AKEB/watercounter/IMG_0184.JPG

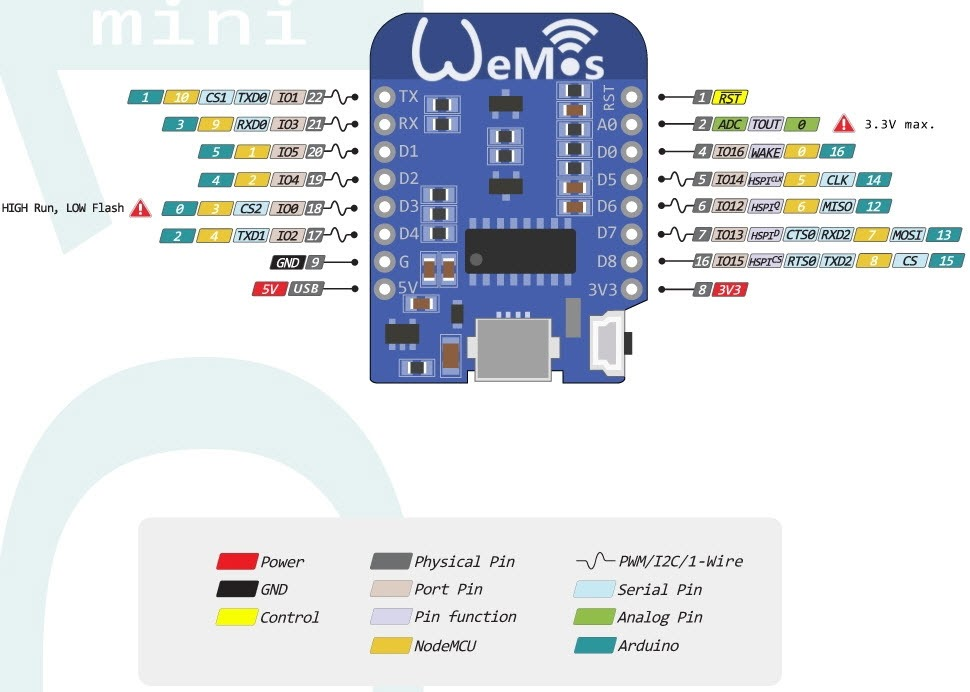
IMG_0184.JPG
