AKEB/watercounter/Photos/IMG_0148.JPG.jpeg

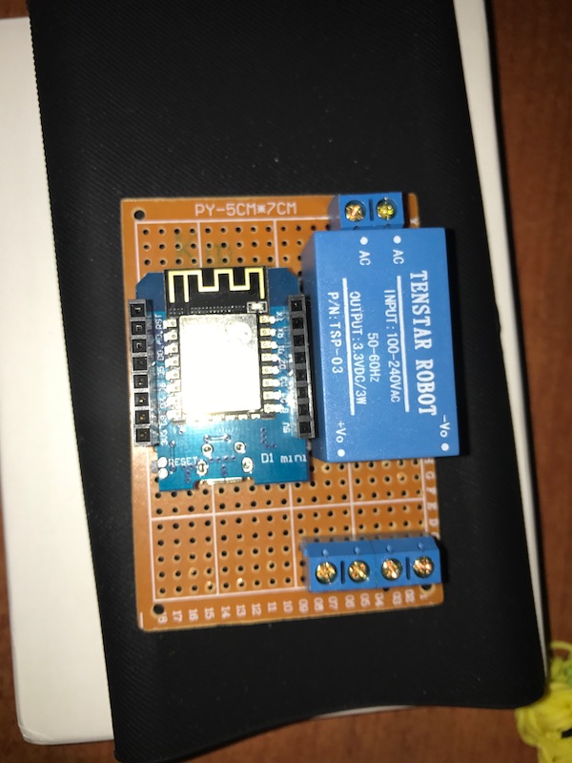
Photos/IMG_0148.JPG.jpeg
