AKEB/watercounter/Photos/IMG_0178.PNG.png

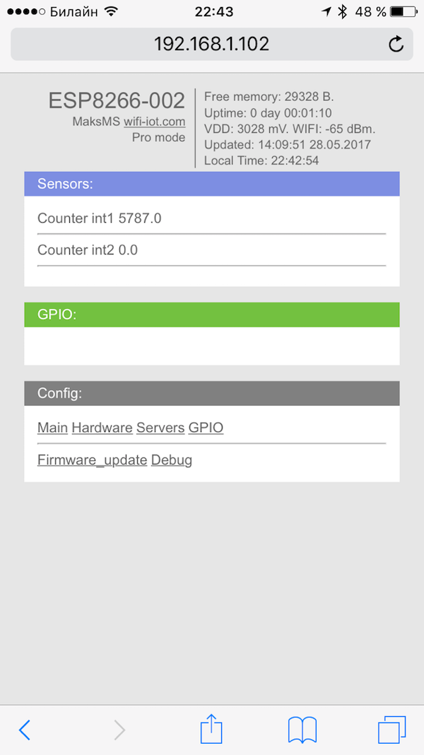
Photos/IMG_0178.PNG.png
