AKEB/watercounter/Photos/IMG_0179.JPG.jpeg

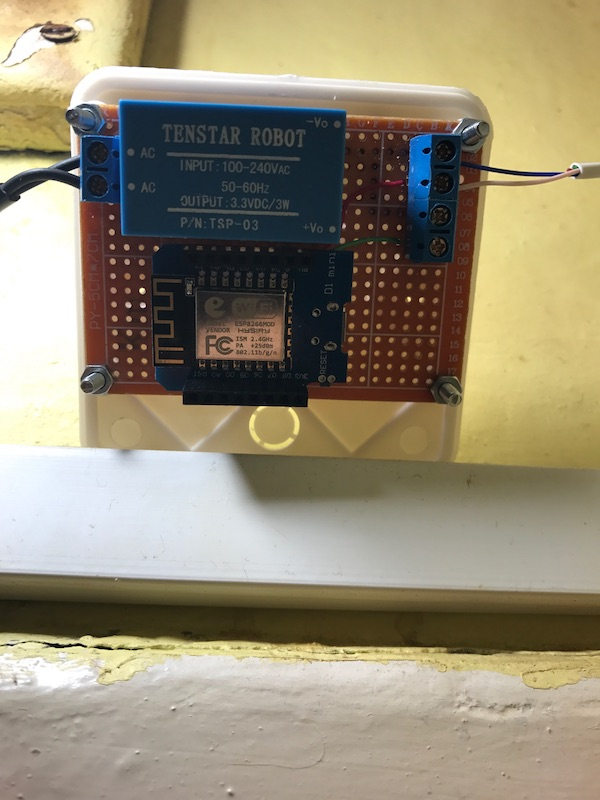
Photos/IMG_0179.JPG.jpeg
