AKEB/watercounter/Photos/IMG_0180.JPG.jpeg

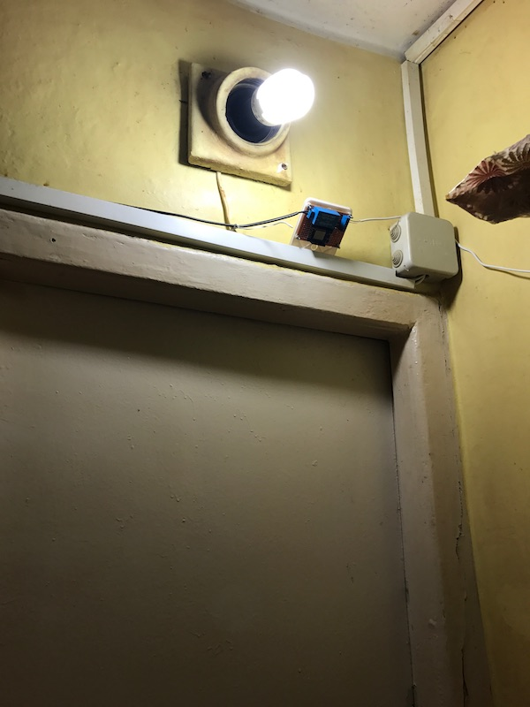
Photos/IMG_0180.JPG.jpeg
