AKEB/watercounter/Photos/IMG_0183.PNG

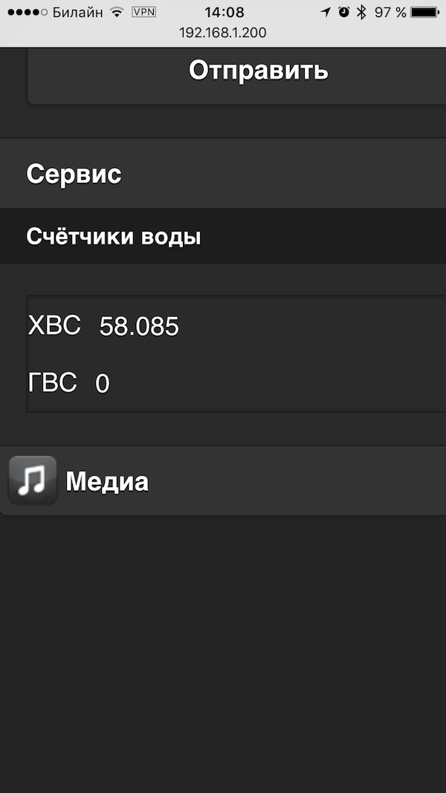
Photos/IMG_0183.PNG
