AKEB/watercounter/Photos/IMG_0248.jpg

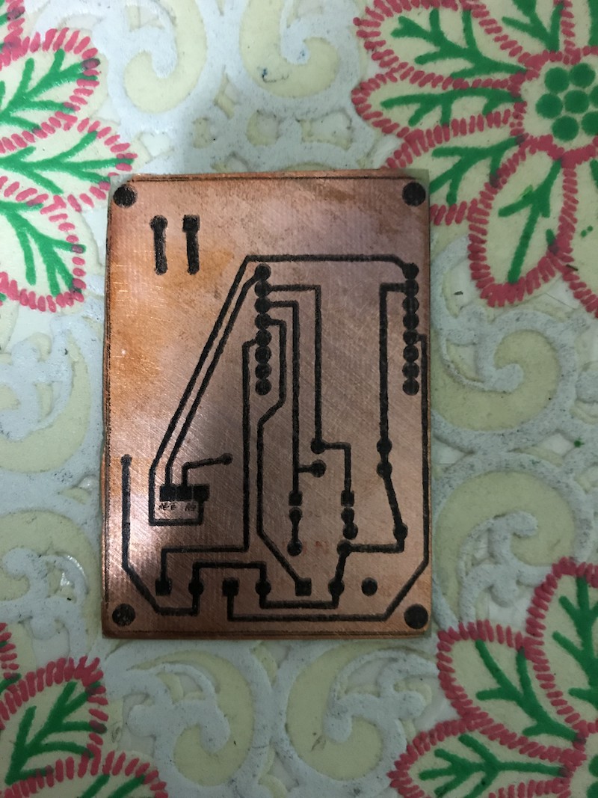
Photos/IMG_0248.jpg
