AKEB/watercounter/Photos/IMG_0249.jpg

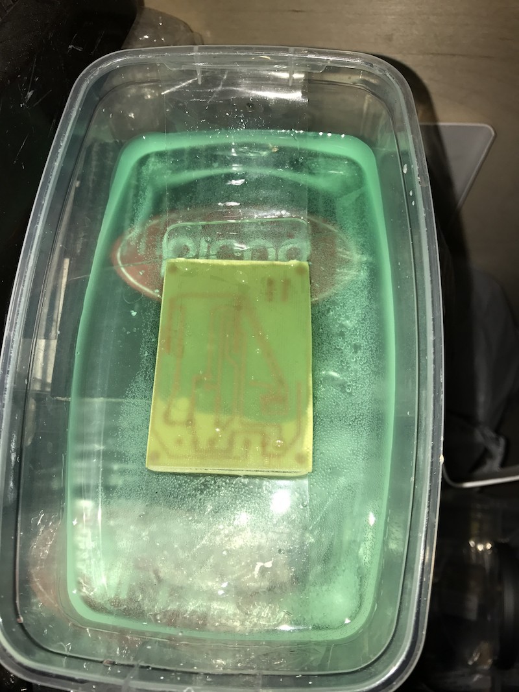
Photos/IMG_0249.jpg
