AKEB/watercounter/Photos/IMG_0250.jpg

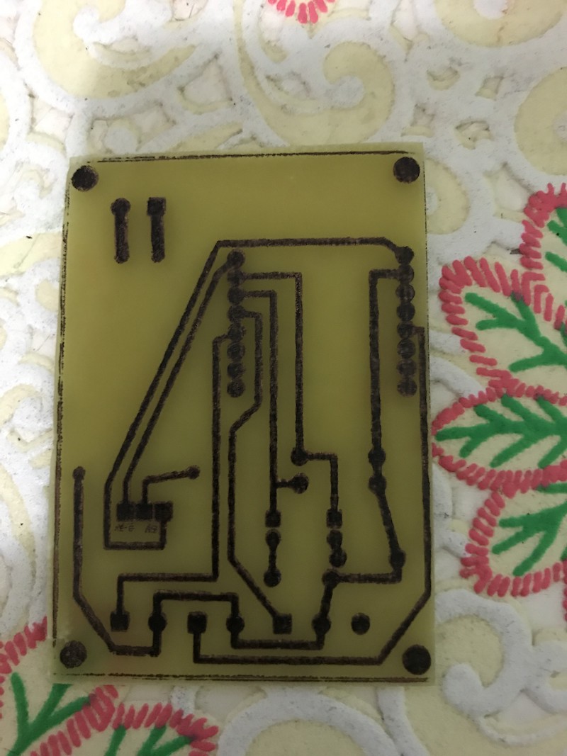
Photos/IMG_0250.jpg
