AKEB/watercounter/Photos/IMG_0251.jpg

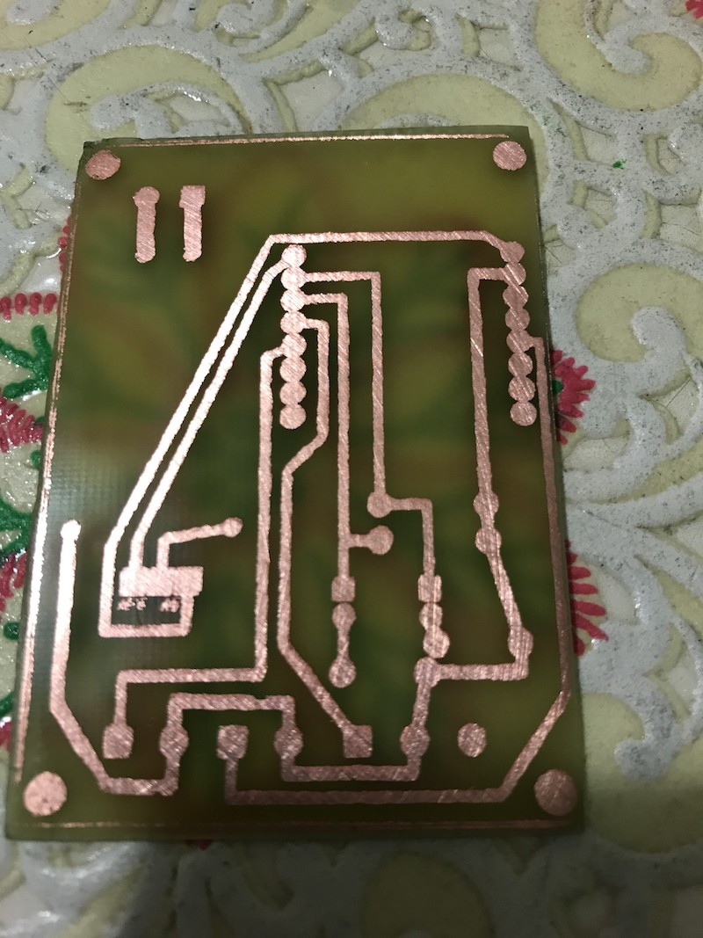
Photos/IMG_0251.jpg
