AKEB/watercounter/Photos/IMG_0252.jpg

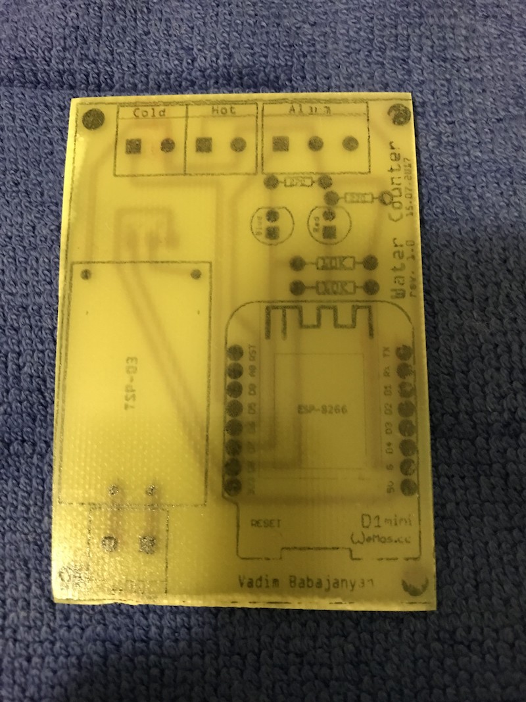
Photos/IMG_0252.jpg
