AKEB/watercounter/Photos/IMG_0253.jpg

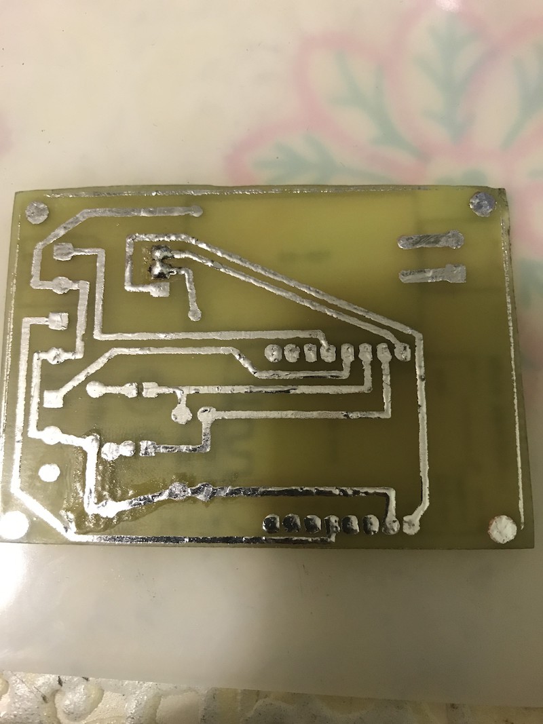
Photos/IMG_0253.jpg
