AKEB/watercounter/Photos/IMG_0255.jpg

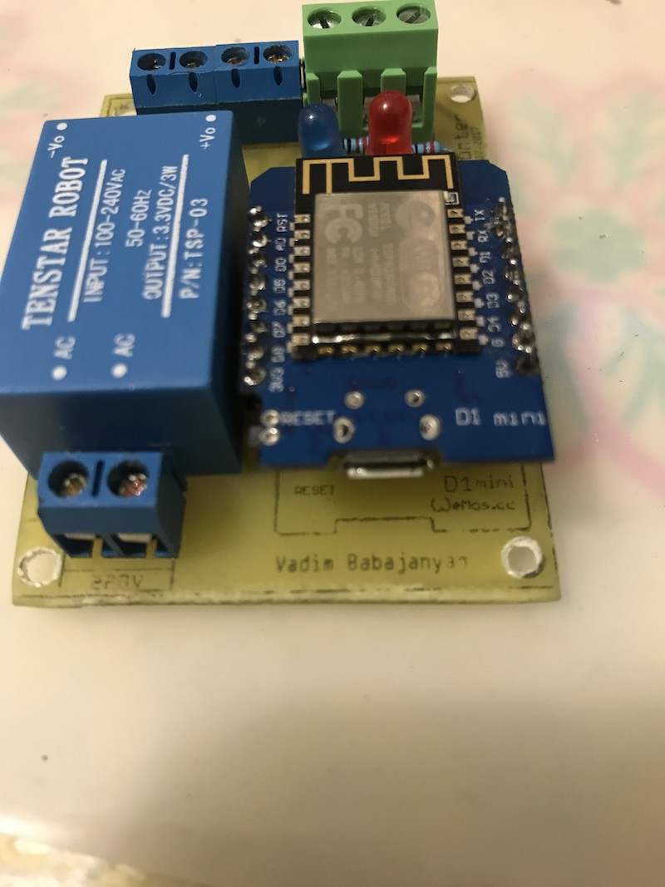
Photos/IMG_0255.jpg
