AKEB/watercounter/Photos/IMG_0256.jpg

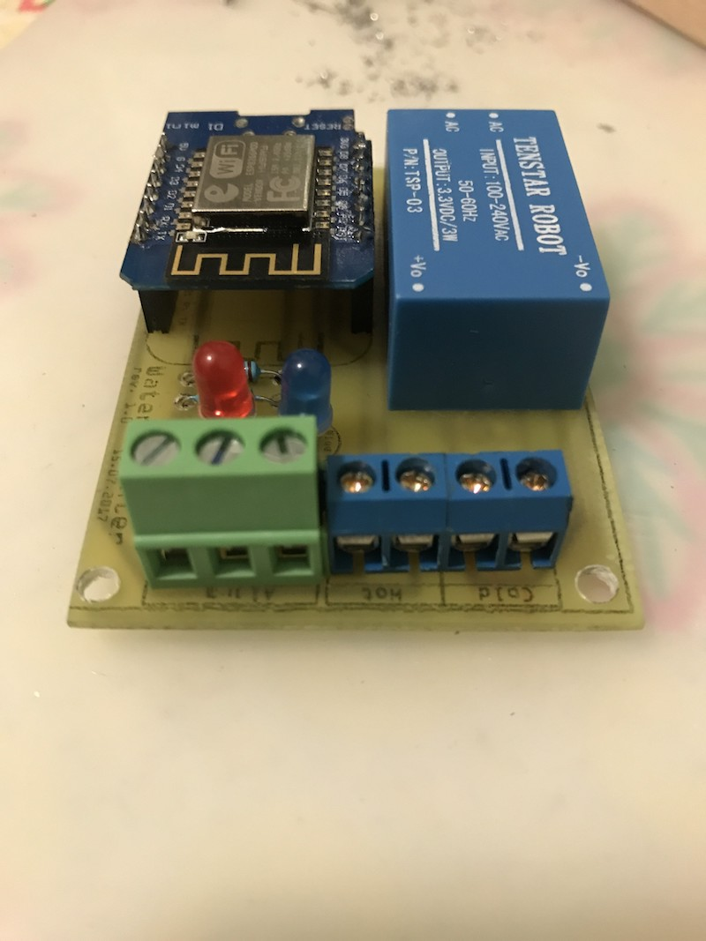
Photos/IMG_0256.jpg
