AKEB/watercounter/Photos/IMG_0257.jpg

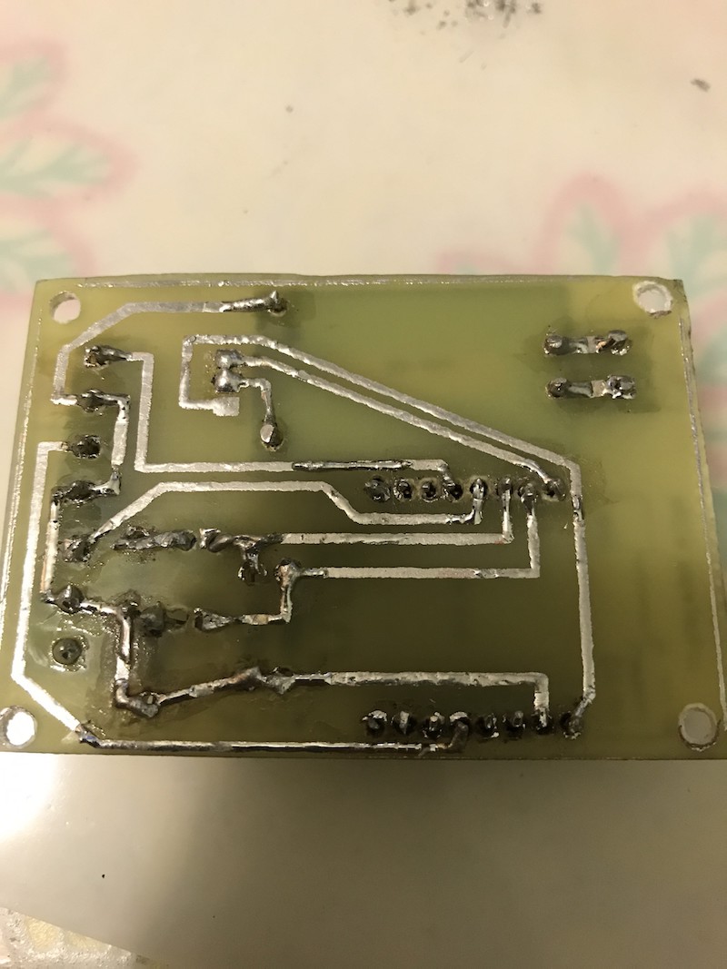
Photos/IMG_0257.jpg
