AKEB/watercounter/PCB/pdf/WaterCounter_etch_silk_bottom.pdf

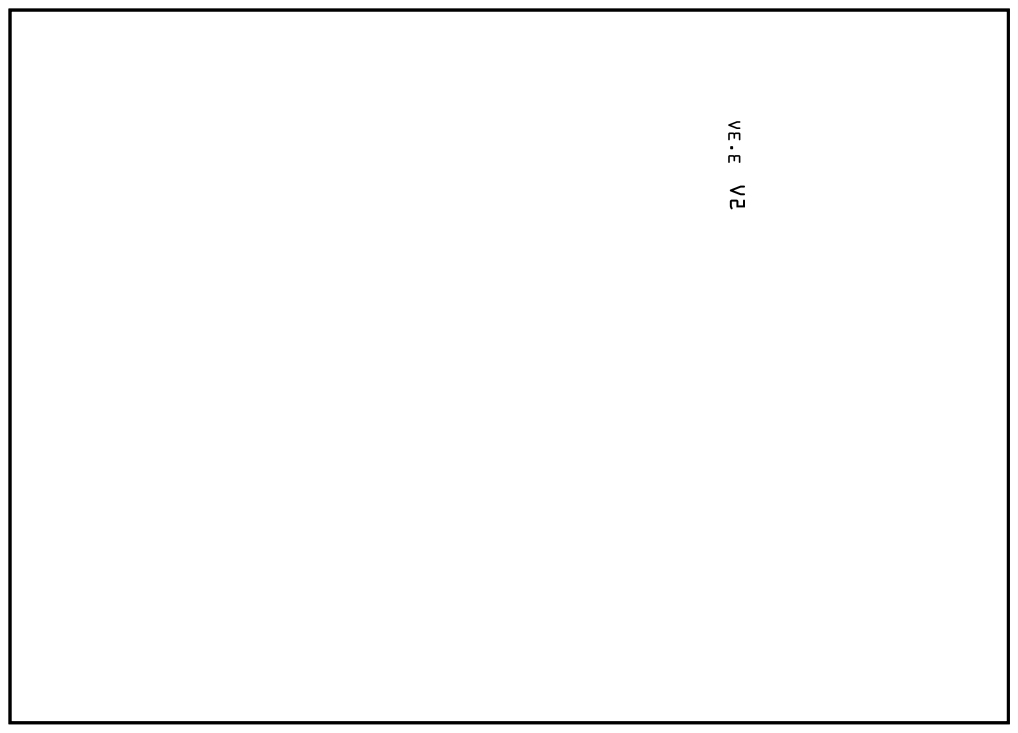
[picture p32: page 1]
