AKEB/watercounter/PCB/pdf/WaterCounter_etch_silk_bottom_mirror.pdf

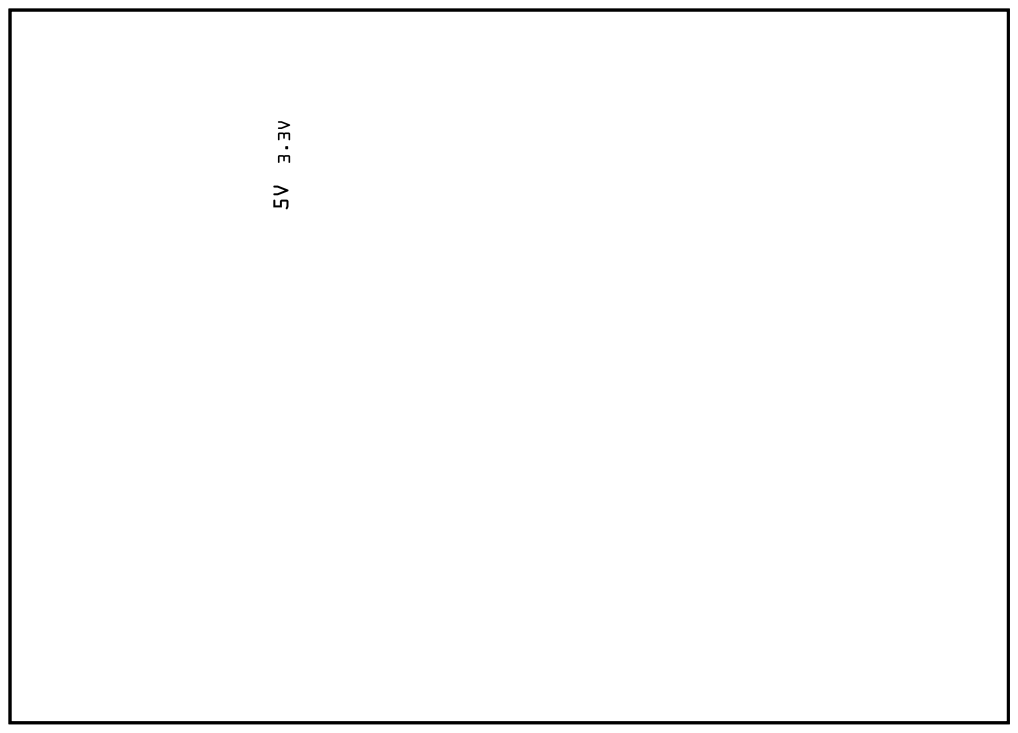
[picture p33: page 1]
