AKEB/watercounter/PCB/pdf/WaterCounter_etch_silk_top.pdf

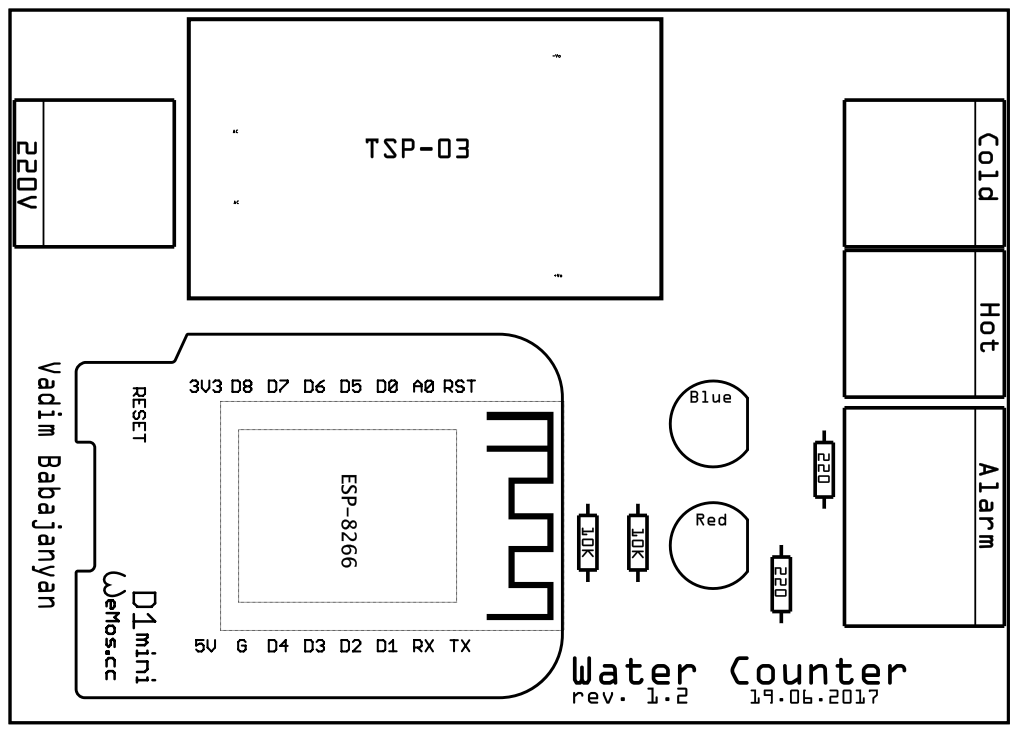
[picture p34: page 1]
