AKEB/watercounter/PCB/pdf/WaterCounter_etch_silk_top_mirror.pdf

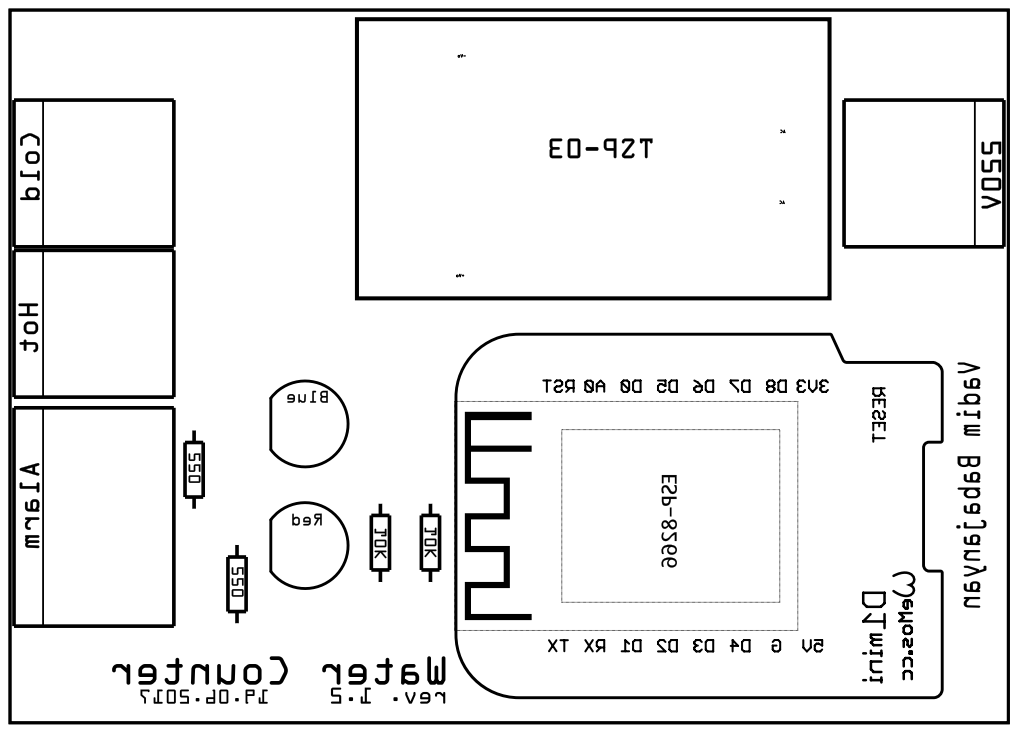
[picture p35: page 1]
