AKEB/watercounter/WaterCounter/FS.ino

// Инициализация FFS
void FS_init(void) {
	SPIFFS.begin();
	{
		Dir dir = SPIFFS.openDir("/");
		while (dir.next()) {
			String fileName = dir.fileName();
			size_t fileSize = dir.fileSize();
		}
	}
	//HTTP страницы для работы с FFS
	//list directory
	HTTP.on("/list", HTTP_GET, handleFileList);
	//загрузка редактора editor
	HTTP.on("/edit", HTTP_GET, []() {
		if(!HTTP.authenticate(_http_user.c_str(), _http_password.c_str())) return HTTP.requestAuthentication();
		if (!handleFileRead("/edit.html")) HTTP.send(404, "text/plain", "FileNotFound");
	});
	//Создание файла
	HTTP.on("/edit", HTTP_PUT, handleFileCreate);
	//Удаление файла
	HTTP.on("/edit", HTTP_DELETE, handleFileDelete);
	//first callback is called after the request has ended with all parsed arguments
	//second callback handles file uploads at that location
	HTTP.on("/edit", HTTP_POST, []() {
		HTTP.send(200, "text/plain", "");
	}, handleFileUpload);
	//called when the url is not defined here
	//use it to load content from SPIFFS
	HTTP.onNotFound([]() {
		if (!handleFileRead(HTTP.uri())) HTTP.send(404, "text/plain", "FileNotFound");
	});
}

// Здесь функции для работы с файловой системой
String getContentType(String filename) {
	if (HTTP.hasArg("download")) return "application/octet-stream";
	else if (filename.endsWith(".htm")) return "text/html";
	else if (filename.endsWith(".html")) return "text/html";
	else if (filename.endsWith(".json")) return "application/json";
	else if (filename.endsWith(".css")) return "text/css";
	else if (filename.endsWith(".js")) return "application/javascript";
	else if (filename.endsWith(".png")) return "image/png";
	else if (filename.endsWith(".gif")) return "image/gif";
	else if (filename.endsWith(".jpg")) return "image/jpeg";
	else if (filename.endsWith(".ico")) return "image/x-icon";
	else if (filename.endsWith(".xml")) return "text/xml";
	else if (filename.endsWith(".pdf")) return "application/x-pdf";
	else if (filename.endsWith(".zip")) return "application/x-zip";
	else if (filename.endsWith(".gz")) return "application/x-gzip";
	return "text/plain";
}

bool handleFileRead(String path) {
	if (path.endsWith("/")) path += "index.html";
	String contentType = getContentType(path);
	String pathWithGz = path + ".gz";
	if (SPIFFS.exists(pathWithGz) || SPIFFS.exists(path)) {
		if (SPIFFS.exists(pathWithGz)) path += ".gz";
		File file = SPIFFS.open(path, "r");
		size_t sent = HTTP.streamFile(file, contentType);
		file.close();
		return true;
	}
	return false;
}

void handleFileUpload() {
	if (HTTP.uri() != "/edit") return;
	HTTPUpload& upload = HTTP.upload();
	if (upload.status == UPLOAD_FILE_START) {
		String filename = upload.filename;
		if (!filename.startsWith("/")) filename = "/" + filename;
		fsUploadFile = SPIFFS.open(filename, "w");
		filename = String();
	} else if (upload.status == UPLOAD_FILE_WRITE) {
		//DBG_OUTPUT_PORT.print("handleFileUpload Data: "); DBG_OUTPUT_PORT.println(upload.currentSize);
		if (fsUploadFile) fsUploadFile.write(upload.buf, upload.currentSize);
	} else if (upload.status == UPLOAD_FILE_END) {
		if (fsUploadFile) fsUploadFile.close();
	}
}

void handleFileDelete() {
	if (HTTP.args() == 0) return HTTP.send(500, "text/plain", "BAD ARGS");
	String path = HTTP.arg(0);
	if (path == "/") return HTTP.send(500, "text/plain", "BAD PATH");
	if (!SPIFFS.exists(path)) return HTTP.send(404, "text/plain", "FileNotFound");
	SPIFFS.remove(path);
	HTTP.send(200, "text/plain", "");
	path = String();
}

void handleFileCreate() {
	if (HTTP.args() == 0) return HTTP.send(500, "text/plain", "BAD ARGS");
	String path = HTTP.arg(0);
	if (path == "/") return HTTP.send(500, "text/plain", "BAD PATH");
	if (SPIFFS.exists(path)) return HTTP.send(500, "text/plain", "FILE EXISTS");
	File file = SPIFFS.open(path, "w");
	if (file) file.close();
	else return HTTP.send(500, "text/plain", "CREATE FAILED");
	HTTP.send(200, "text/plain", "");
	path = String();
}

void handleFileList() {
	if (!HTTP.hasArg("dir")) {
		HTTP.send(500, "text/plain", "BAD ARGS");
		return;
	}
	String path = HTTP.arg("dir");
	Dir dir = SPIFFS.openDir(path);
	path = String();
	String output = "[";
	while (dir.next()) {
		File entry = dir.openFile("r");
		if (output != "[") output += ',';
		bool isDir = false;
		output += "{\"type\":\"";
		output += (isDir) ? "dir" : "file";
		output += "\",\"name\":\"";
		output += String(entry.name()).substring(1);
		output += "\"}";
		entry.close();
	}
	output += "]";
	HTTP.send(200, "text/json", output);
}
